uecken/xiao-coin/img/xiao-coin_v0.4_difference.png

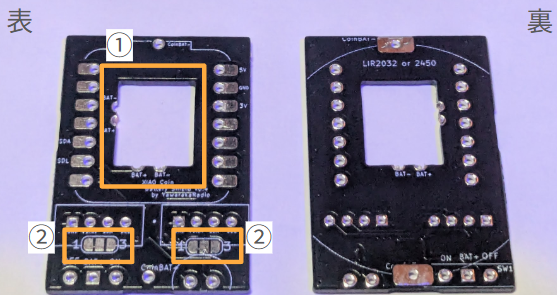
img/xiao-coin_v0.4_difference.png
