uecken/xiao-coin/img/XIAO_Castlated-Hole.jpg

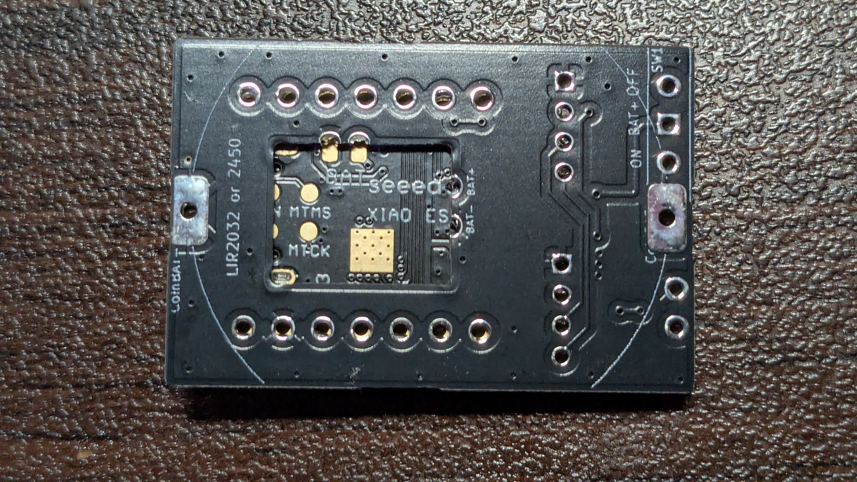
img/XIAO_Castlated-Hole.jpg
