uecken/xiao-coin/img_micropython/Thonny_Select_Options.png

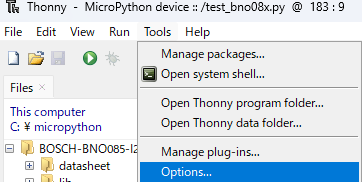
img_micropython/Thonny_Select_Options.png
