uecken/xiao-coin/XIAO_ButtonBatteryPCB_Pulic/3D/grove-connectors-stand-and-flat-male-plugs-1.snapshot.44/images/sit_back.PNG

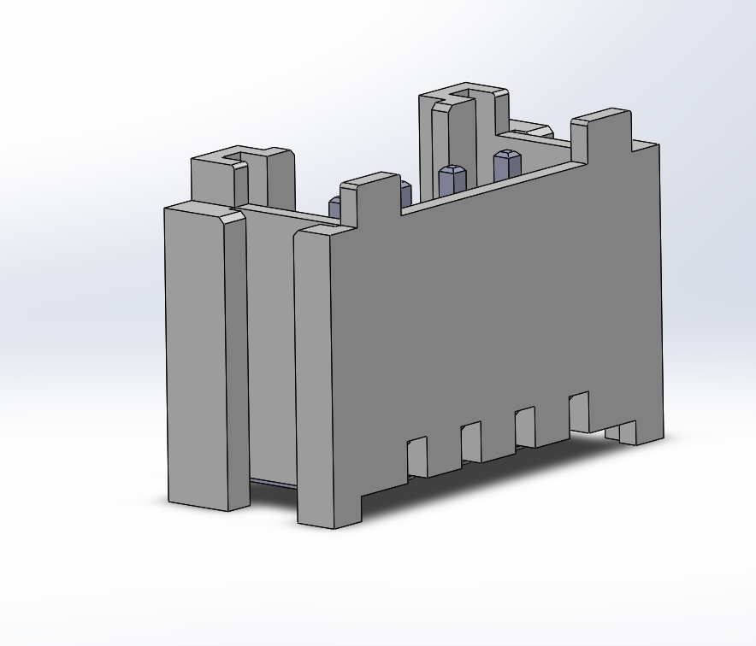
XIAO_ButtonBatteryPCB_Pulic/3D/grove-connectors-stand-and-flat-male-plugs-1.snapshot.44/images/sit_back.PNG
