uecken/xiao-coin/XIAO_ButtonBatteryPCB_Pulic/3D/grove-ultrasonic-ranger-v2-0-1.snapshot.4/render.png

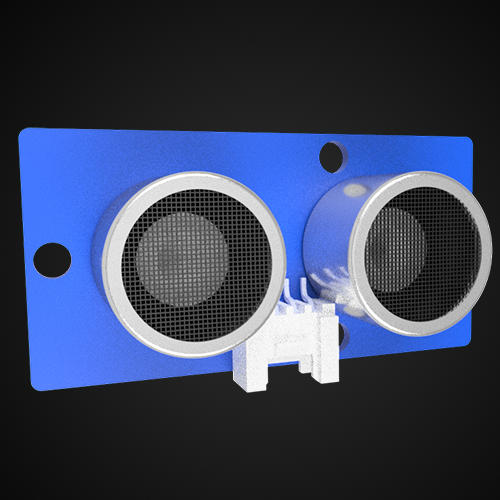
XIAO_ButtonBatteryPCB_Pulic/3D/grove-ultrasonic-ranger-v2-0-1.snapshot.4/render.png
