uecken/xiao-coin/XIAO_ButtonBatteryPCB_Pulic/3D/hc-sr04-ultrasonic-sensor-4.snapshot.4/HCSR04.jpg

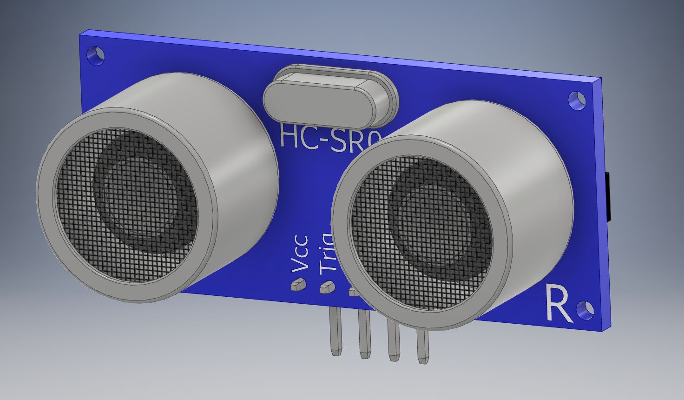
XIAO_ButtonBatteryPCB_Pulic/3D/hc-sr04-ultrasonic-sensor-4.snapshot.4/HCSR04.jpg
