uecken/xiao-coin/XIAO_ButtonBatteryPCB_Pulic/3D/raspberry-pi-pico-w-1.snapshot.4/Screenshot 2023-02-27 193411.png

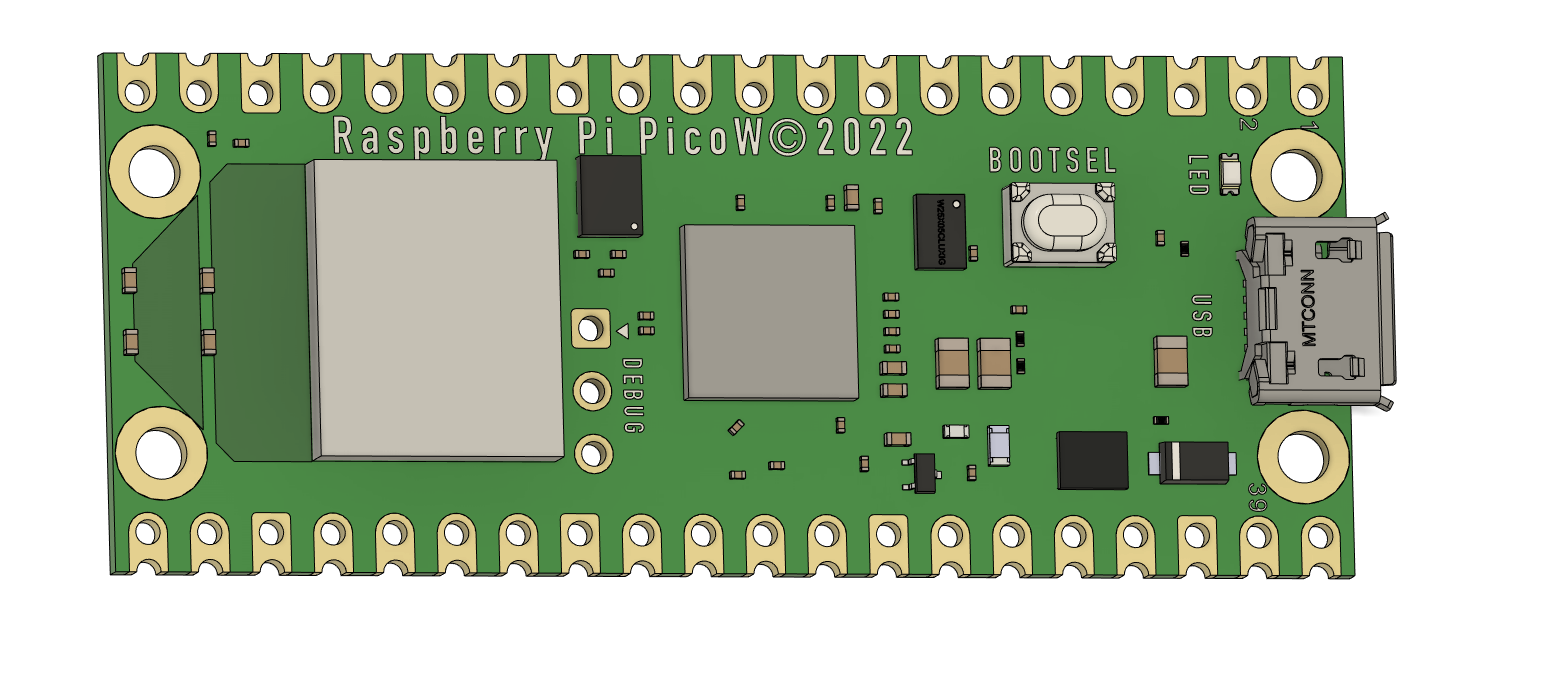
XIAO_ButtonBatteryPCB_Pulic/3D/raspberry-pi-pico-w-1.snapshot.4/Screenshot 2023-02-27 193411.png
