uecken/xiao-coin/XIAO_ButtonBatteryPCB_Pulic/3D/seeed-studio-xiao-esp32-c6-1.snapshot.3/Front Side.png

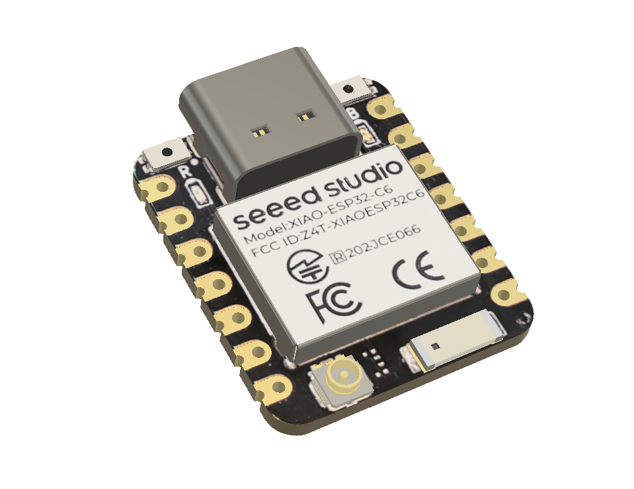
XIAO_ButtonBatteryPCB_Pulic/3D/seeed-studio-xiao-esp32-c6-1.snapshot.3/Front Side.png
