uecken/xiao-coin/XIAO_ButtonBatteryPCB_Pulic/3D/seeed-studio-xiao-esp32-c6-1.snapshot.3/Seeed_Studio_XIAO_ESP32-C6_2024-Nov-07_07-47-43AM-000_CustomizedView10174300734.png

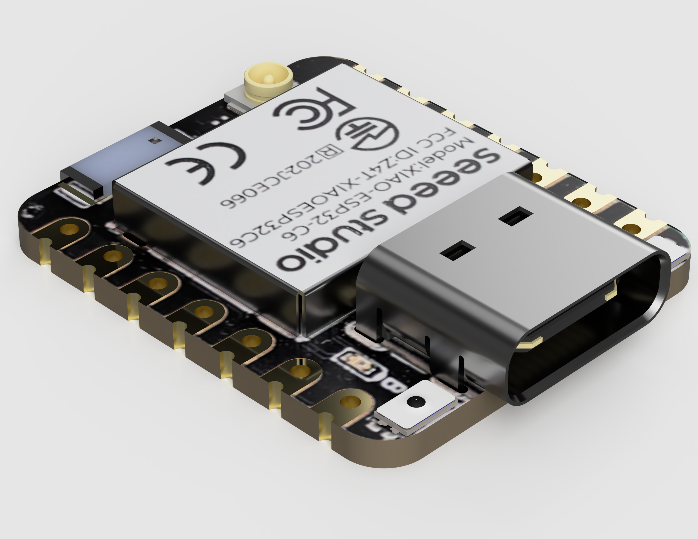
XIAO_ButtonBatteryPCB_Pulic/3D/seeed-studio-xiao-esp32-c6-1.snapshot.3/Seeed_Studio_XIAO_ESP32-C6_2024-Nov-07_07-47-43AM-000_CustomizedView10174300734.png
