uecken/xiao-coin/XIAO_ButtonBatteryPCB_Pulic/3D/spresense-board-3d-model-1.snapshot.3/Spresense Board .png

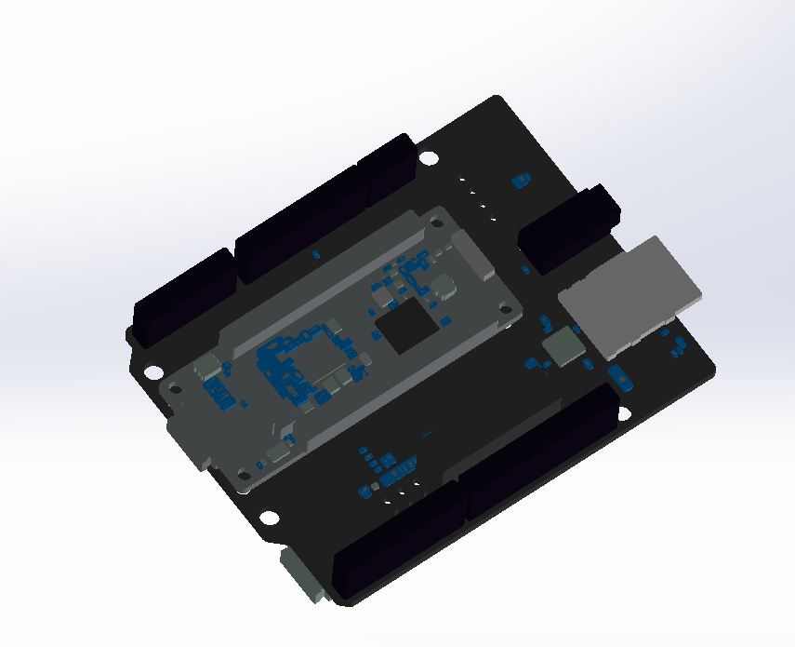
XIAO_ButtonBatteryPCB_Pulic/3D/spresense-board-3d-model-1.snapshot.3/Spresense Board .png
