uecken/xiao-coin/XIAO_ButtonBatteryPCB_Pulic/production/XIAO_ButtonBatteryPCB.jpg

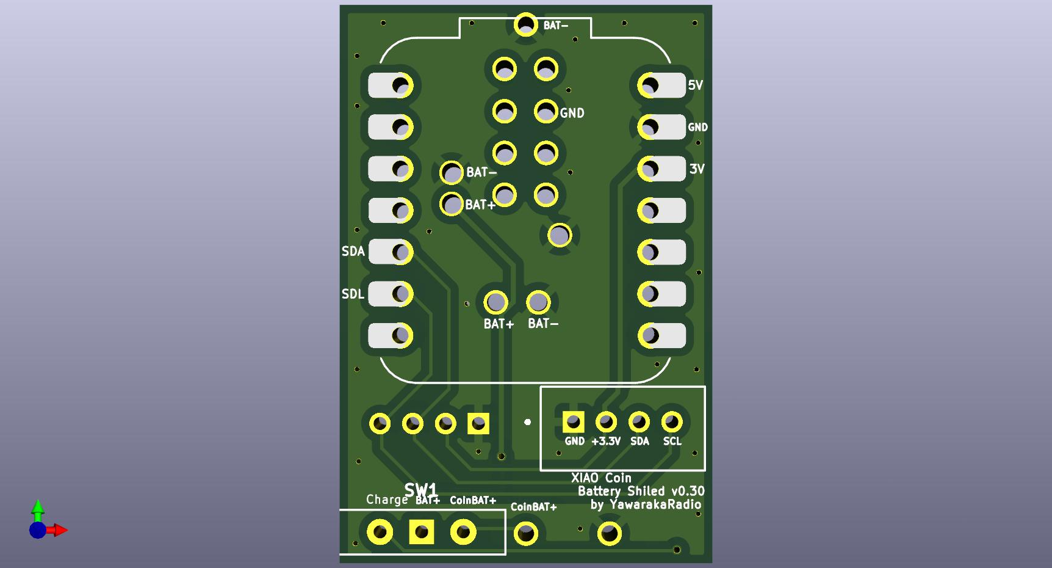
XIAO_ButtonBatteryPCB_Pulic/production/XIAO_ButtonBatteryPCB.jpg
