uecken/xiao-coin/XIAO_ButtonBatteryPCB_Pulic/3D/raspberry-pi-pico-r3-1.snapshot.2/U3, W25Q16JVUXIQ, Serial NOR Flash 16 Mbit, Raspberry Pi Pico-R3.SLDPRT

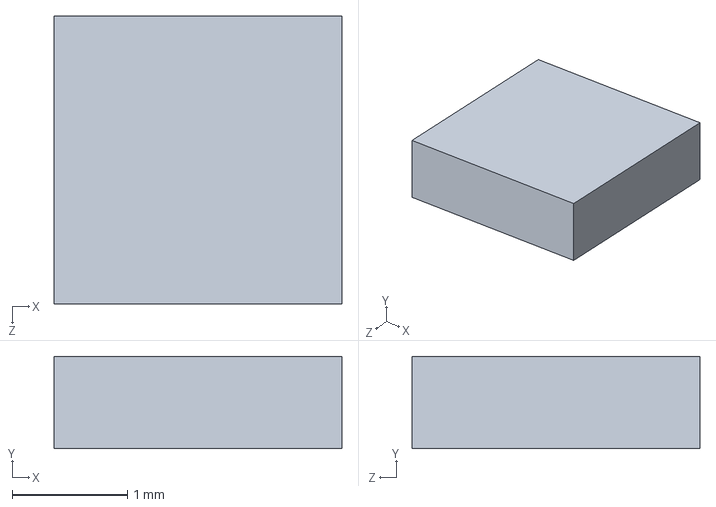
[picture p60: CAD file, 2025-05-27]
XIAO_ButtonBatteryPCB_Pulic/3D/raspberry-pi-pico-r3-1.snapshot.2/U3, W25Q16JVUXIQ, Serial NOR Flash 16 Mbit, Raspberry Pi Pico-R3.SLDPRT
2.50 x 0.8 x 2.50 mm
