uecken/xiao-coin/XIAO_ButtonBatteryPCB_Pulic/3D/grove-connectors-stand-and-flat-male-plugs-1.snapshot.44/Grove Connector (flat).STEP

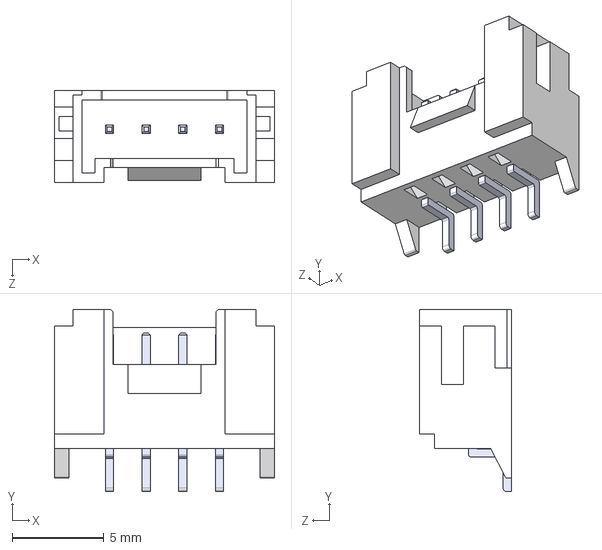
[picture p61: CAD file, 2025-05-27]
XIAO_ButtonBatteryPCB_Pulic/3D/grove-connectors-stand-and-flat-male-plugs-1.snapshot.44/Grove Connector (flat).STEP
12.0 x 9.95 x 5.00 mm
