uecken/xiao-coin/XIAO_ButtonBatteryPCB_Pulic/3D/raspberry-pi-pico-r3-1.snapshot.2/X1, X12M000000S096, 12 Mhz Crystal Resonator, Raspberry Pi Pico-R3.SLDPRT

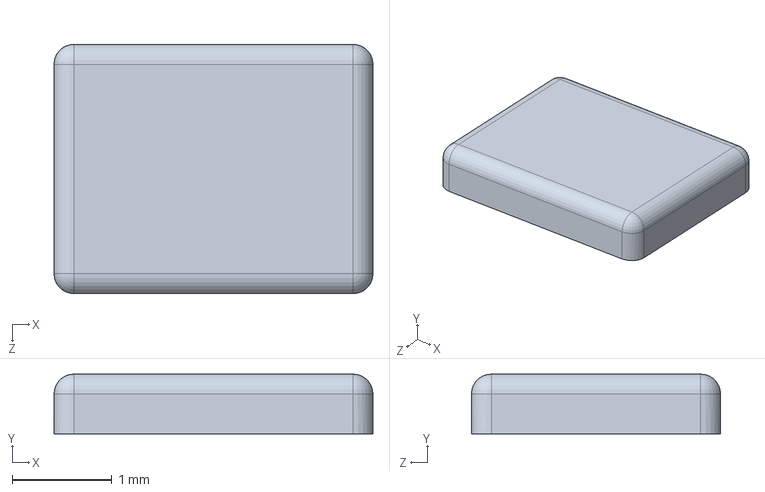
[picture p63: CAD file, 2025-05-27]
XIAO_ButtonBatteryPCB_Pulic/3D/raspberry-pi-pico-r3-1.snapshot.2/X1, X12M000000S096, 12 Mhz Crystal Resonator, Raspberry Pi Pico-R3.SLDPRT
3.20 x 0.6 x 2.50 mm
