uecken/xiao-coin/XIAO_ButtonBatteryPCB_Pulic/3D/grove-connectors-stand-and-flat-male-plugs-1.snapshot.44/Grove Connector (standing).STEP

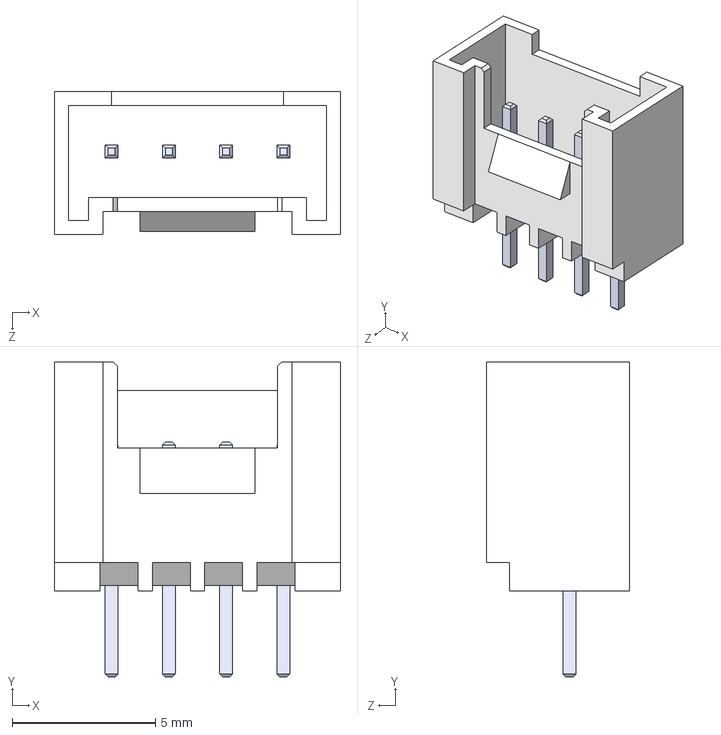
[picture p64: CAD file, 2025-05-27]
XIAO_ButtonBatteryPCB_Pulic/3D/grove-connectors-stand-and-flat-male-plugs-1.snapshot.44/Grove Connector (standing).STEP
10.0 x 11.0 x 5.00 mm
