uecken/xiao-coin/XIAO_ButtonBatteryPCB_Pulic/3D/raspberry-pi-pico-r3-1.snapshot.2/Q1, MOSFET, DMG1012T, Raspberry Pi Pico-R3.SLDPRT

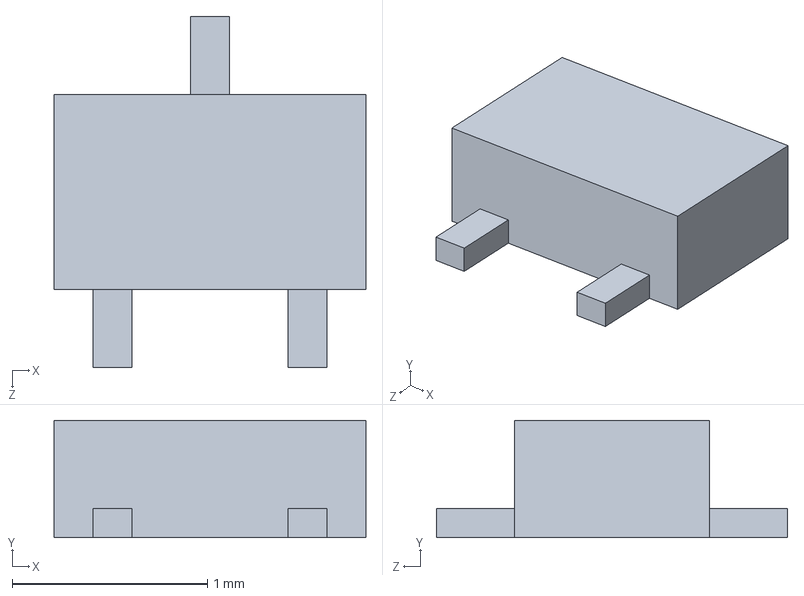
[picture p66: CAD file, 2025-05-27]
XIAO_ButtonBatteryPCB_Pulic/3D/raspberry-pi-pico-r3-1.snapshot.2/Q1, MOSFET, DMG1012T, Raspberry Pi Pico-R3.SLDPRT
1.60 x 0.6 x 1.80 mm
