uecken/xiao-coin/XIAO_ButtonBatteryPCB_Pulic/3D/raspberry-pi-pico-r3-1.snapshot.2/D1, Diode, Schottky, Raspberry Pi Pico-R3.SLDPRT

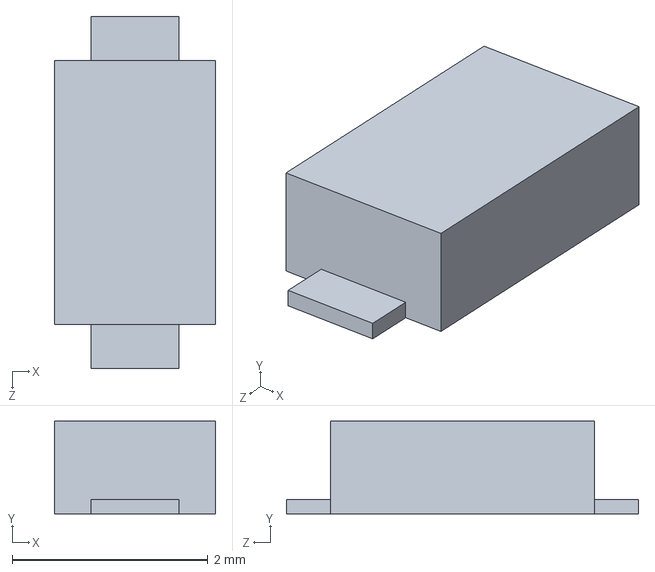
[picture p68: CAD file, 2025-05-27]
XIAO_ButtonBatteryPCB_Pulic/3D/raspberry-pi-pico-r3-1.snapshot.2/D1, Diode, Schottky, Raspberry Pi Pico-R3.SLDPRT
1.65 x 0.95 x 3.60 mm
