uecken/xiao-coin/XIAO_ButtonBatteryPCB_Pulic/3D/raspberry-pi-pico-r3-1.snapshot.2/SMD Resistor, Configurable, Raspberry Pi Pico-R3.SLDPRT

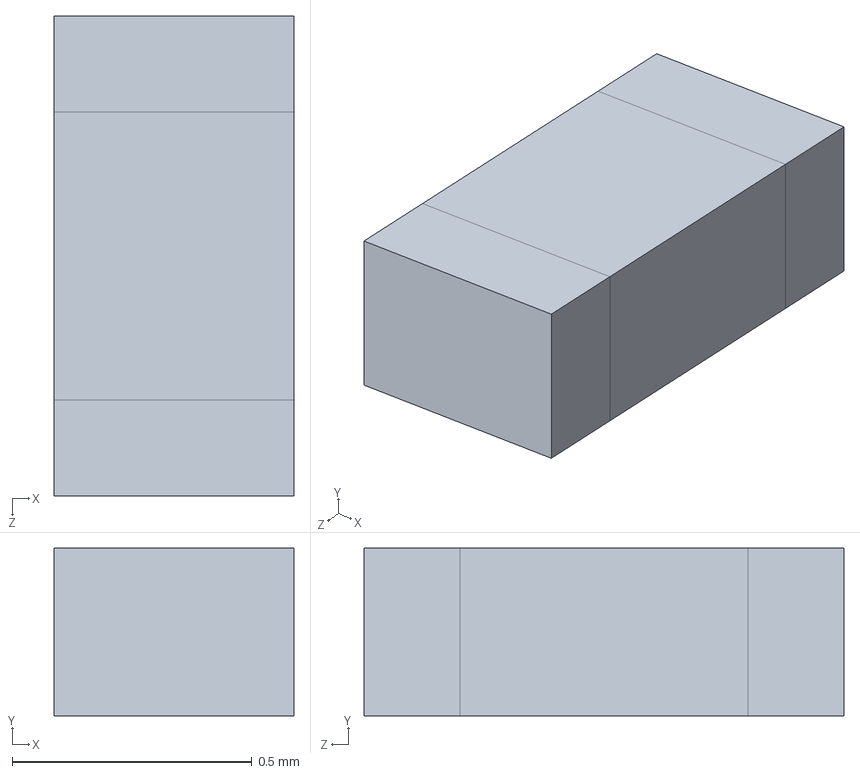
[picture p71: CAD file, 2025-05-27]
XIAO_ButtonBatteryPCB_Pulic/3D/raspberry-pi-pico-r3-1.snapshot.2/SMD Resistor, Configurable, Raspberry Pi Pico-R3.SLDPRT
0.5 x 0.35 x 1.00 mm
