uecken/xiao-coin/XIAO_ButtonBatteryPCB_Pulic/3D/raspberry-pi-pico-r3-1.snapshot.2/PCB, Raspberry Pi Pico-R3.SLDPRT

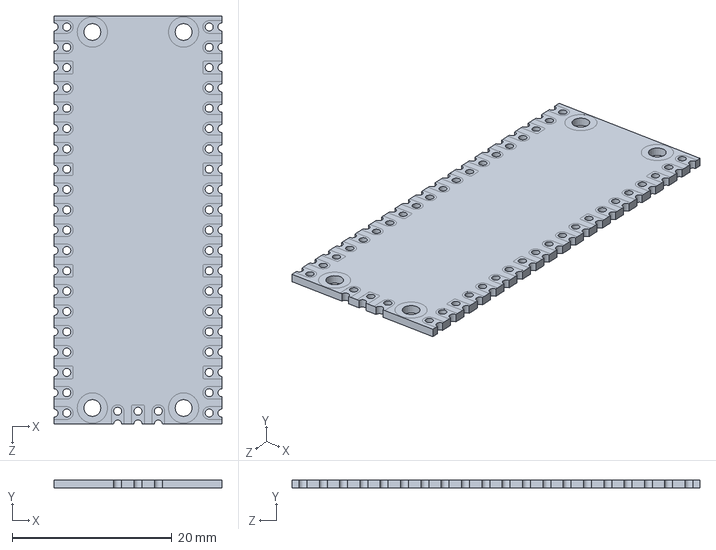
[picture p73: CAD file, 2025-05-27]
XIAO_ButtonBatteryPCB_Pulic/3D/raspberry-pi-pico-r3-1.snapshot.2/PCB, Raspberry Pi Pico-R3.SLDPRT
21.0 x 1.00 x 51.0 mm
