uecken/xiao-coin/XIAO_ButtonBatteryPCB_Pulic/3D/pin-header-male-2-54mm-different-pin-numbers-1.snapshot.2/10-Pin Header - Male - 2.54mm.step

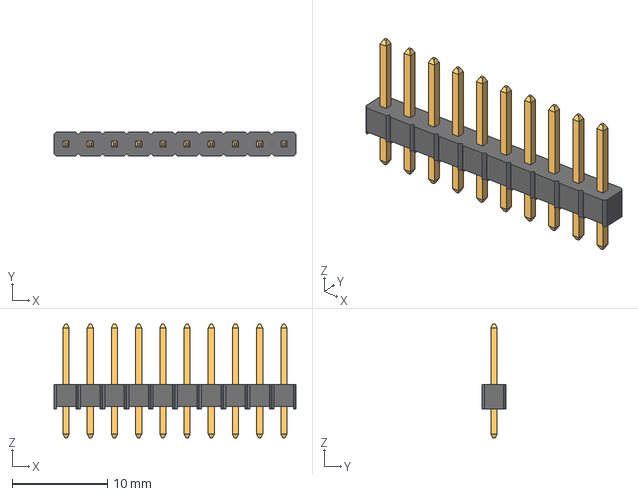
[picture p76: CAD file, 2025-05-27]
XIAO_ButtonBatteryPCB_Pulic/3D/pin-header-male-2-54mm-different-pin-numbers-1.snapshot.2/10-Pin Header - Male - 2.54mm.step
25.4 x 2.54 x 11.9 mm
