uecken/xiao-coin/XIAO_ButtonBatteryPCB_Pulic/3D/raspberry-pi-pico-r3-1.snapshot.2/D2, QSME-C194, LED, Raspberry Pi Pico-R3.SLDPRT

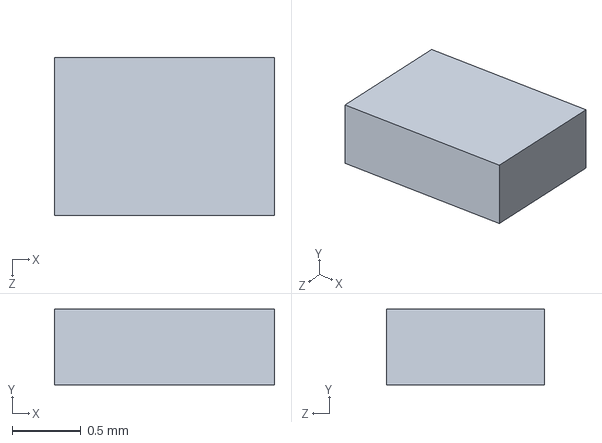
[picture p77: CAD file, 2025-05-27]
XIAO_ButtonBatteryPCB_Pulic/3D/raspberry-pi-pico-r3-1.snapshot.2/D2, QSME-C194, LED, Raspberry Pi Pico-R3.SLDPRT
1.60 x 0.55 x 1.15 mm
