uecken/xiao-coin/XIAO_ButtonBatteryPCB_Pulic/3D/raspberry-pi-pico-r3-1.snapshot.2/MicroUSB Port, Raspberry Pi Pico-R3.SLDPRT

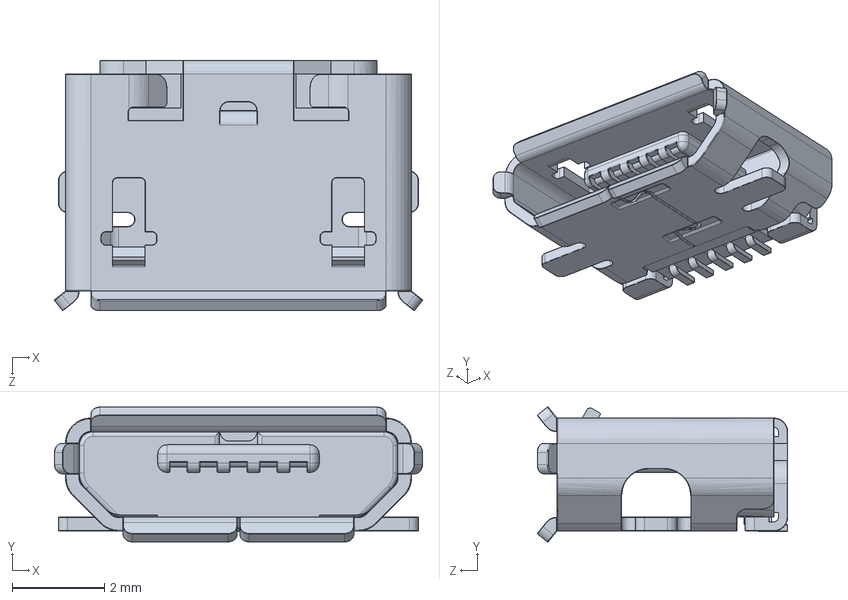
[picture p79: CAD file, 2025-05-27]
XIAO_ButtonBatteryPCB_Pulic/3D/raspberry-pi-pico-r3-1.snapshot.2/MicroUSB Port, Raspberry Pi Pico-R3.SLDPRT
7.97 x 2.92 x 5.43 mm
