uecken/xiao-coin/XIAO_ButtonBatteryPCB_Pulic/3D/raspberry-pi-pico-r3-1.snapshot.2/L1, Inductor, Raspberry Pi Pico-R3.SLDPRT

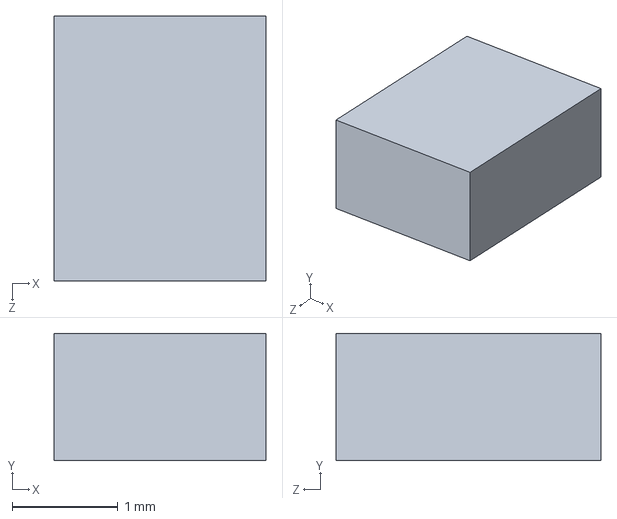
[picture p82: CAD file, 2025-05-27]
XIAO_ButtonBatteryPCB_Pulic/3D/raspberry-pi-pico-r3-1.snapshot.2/L1, Inductor, Raspberry Pi Pico-R3.SLDPRT
2.00 x 1.20 x 2.50 mm
