uecken/xiao-coin/XIAO_ButtonBatteryPCB_Pulic/3D/raspberry-pi-pico-r3-1.snapshot.2/SW1, Tact Switch, Raspberry Pi Pico-R3.SLDPRT

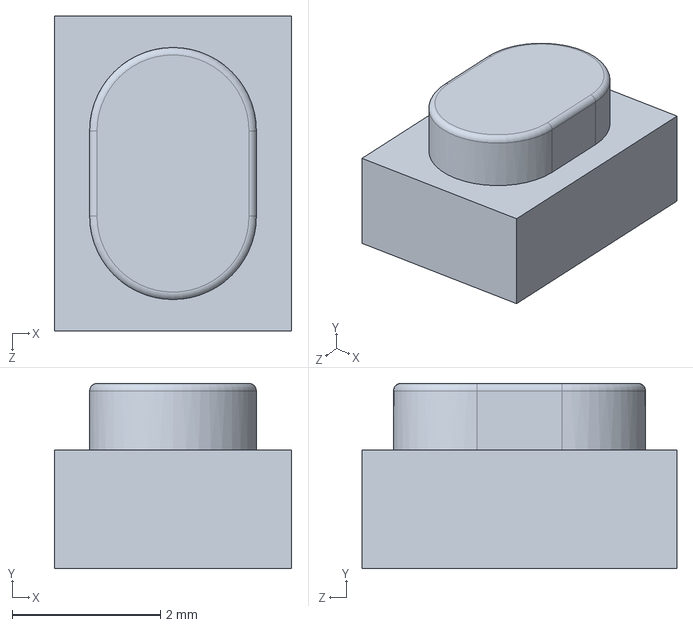
[picture p84: CAD file, 2025-05-27]
XIAO_ButtonBatteryPCB_Pulic/3D/raspberry-pi-pico-r3-1.snapshot.2/SW1, Tact Switch, Raspberry Pi Pico-R3.SLDPRT
3.20 x 2.50 x 4.25 mm
