uecken/xiao-coin/XIAO_ButtonBatteryPCB_Pulic/3D/pin-header-male-2-54mm-different-pin-numbers-1.snapshot.2/3-Pin Header - Male - 2.54mm.step

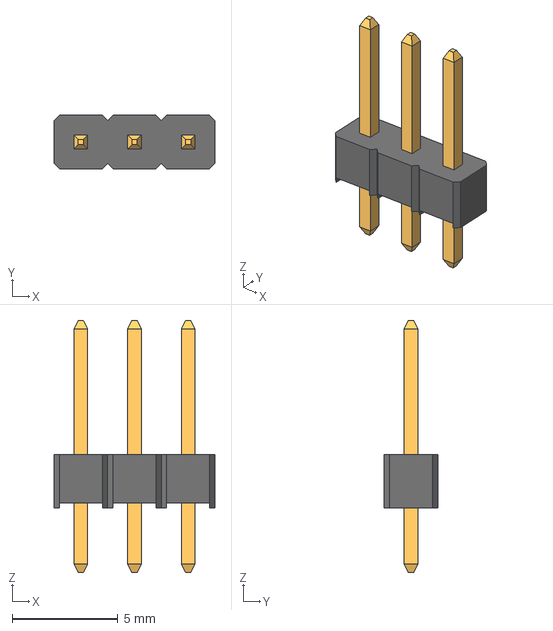
[picture p87: CAD file, 2025-05-27]
XIAO_ButtonBatteryPCB_Pulic/3D/pin-header-male-2-54mm-different-pin-numbers-1.snapshot.2/3-Pin Header - Male - 2.54mm.step
7.62 x 2.54 x 11.9 mm
